facundolucianna/CESE-7maCorte-DCI/3DPictures/01BlueFront.jpg

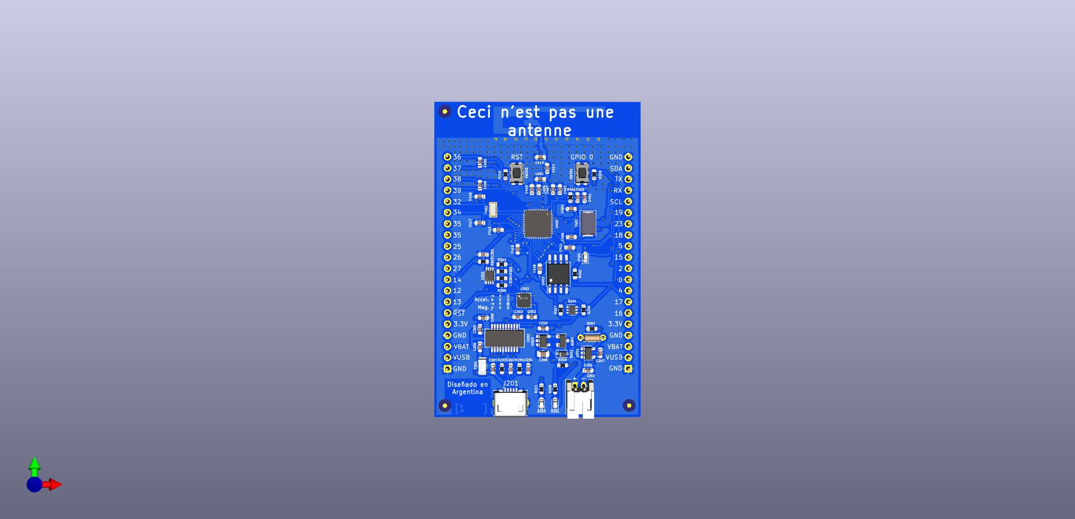
3DPictures/01BlueFront.jpg
