facundolucianna/CESE-7maCorte-DCI/3DPictures/02BlueFrontDetail.jpg

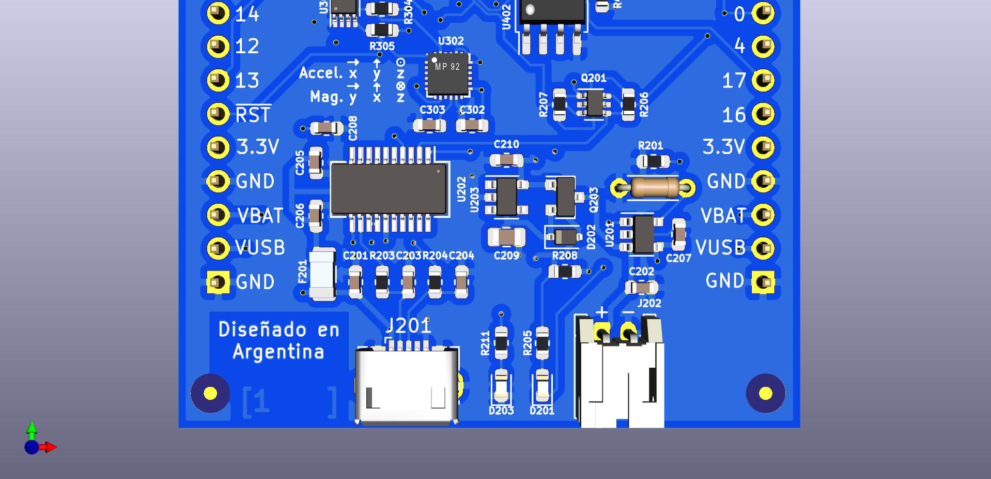
3DPictures/02BlueFrontDetail.jpg
