facundolucianna/CESE-7maCorte-DCI/3DPictures/03BlueBack.jpg

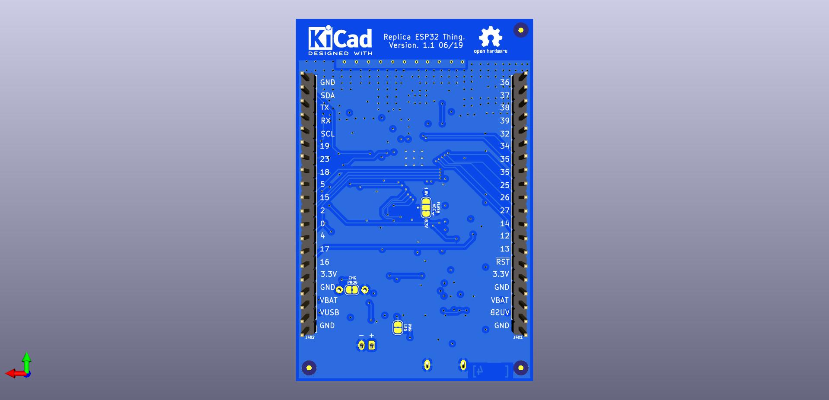
3DPictures/03BlueBack.jpg
