facundolucianna/CESE-7maCorte-DCI/3DPictures/04BlueBackDetail.jpg

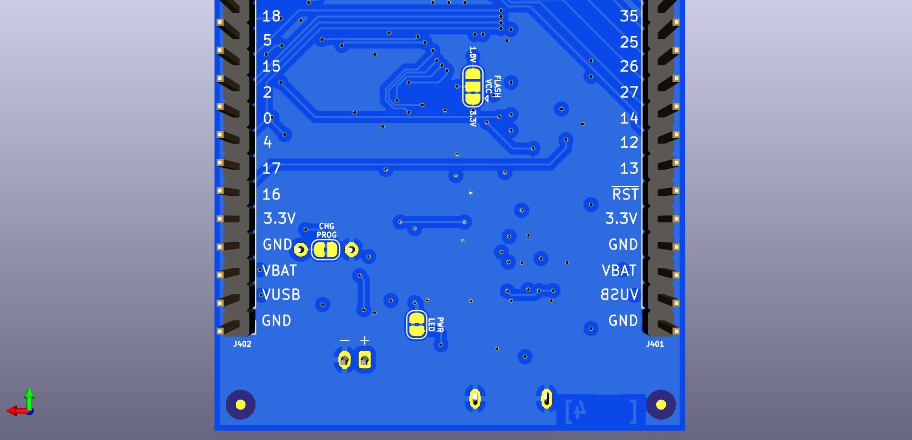
3DPictures/04BlueBackDetail.jpg
