facundolucianna/CESE-7maCorte-DCI/3DPictures/05BlueWeirdAngle.jpg

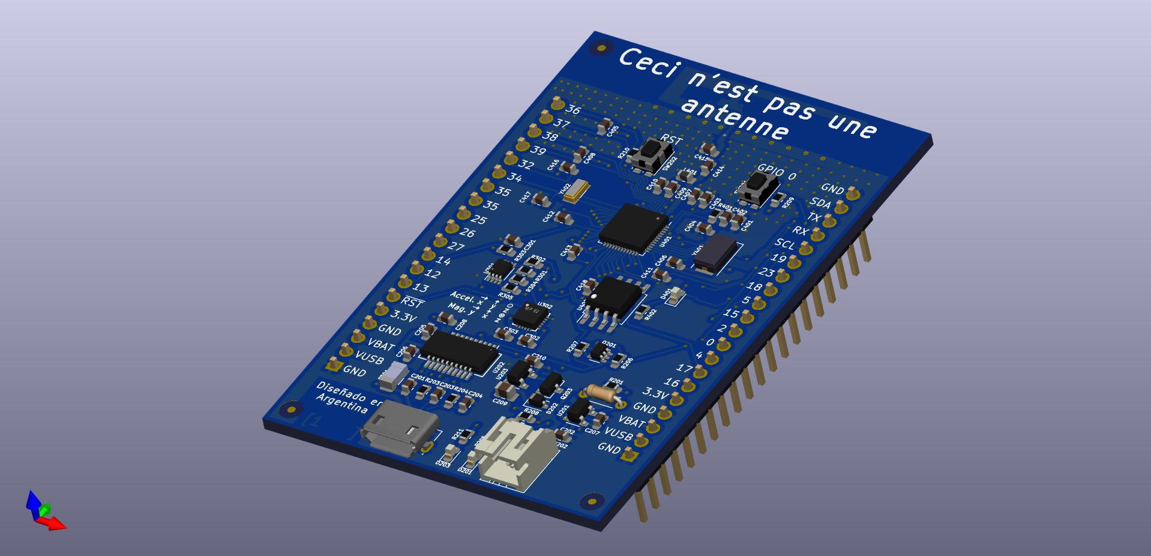
3DPictures/05BlueWeirdAngle.jpg
