facundolucianna/CESE-7maCorte-DCI/3DPictures/06BlueAnotherWeirdAngle.jpg

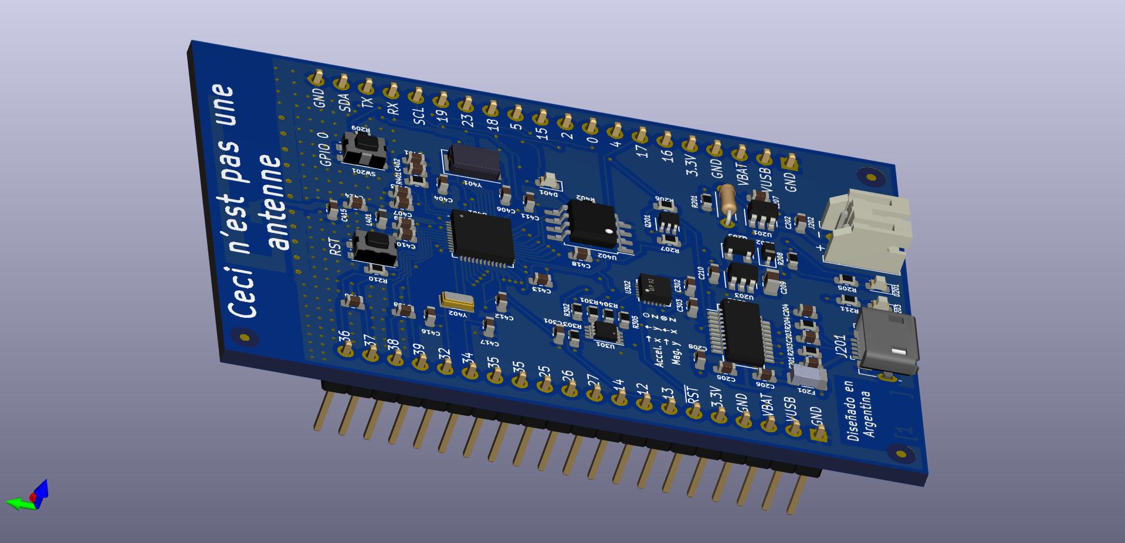
3DPictures/06BlueAnotherWeirdAngle.jpg
