facundolucianna/CESE-7maCorte-DCI/3DPictures/08cheapVersionWeirdAngle.jpg

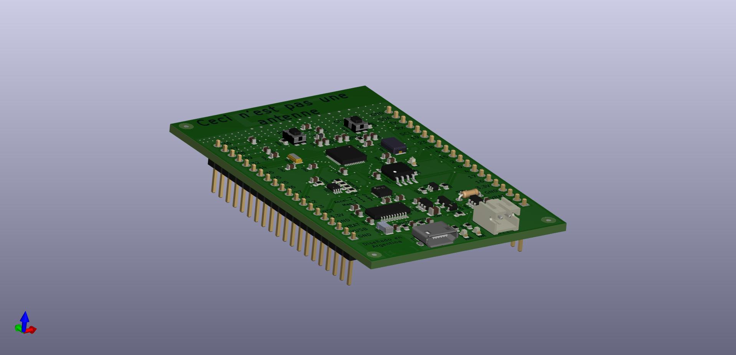
3DPictures/08cheapVersionWeirdAngle.jpg
