facundolucianna/CESE-7maCorte-DCI/3DPictures/09SparfunVersionFront.jpg

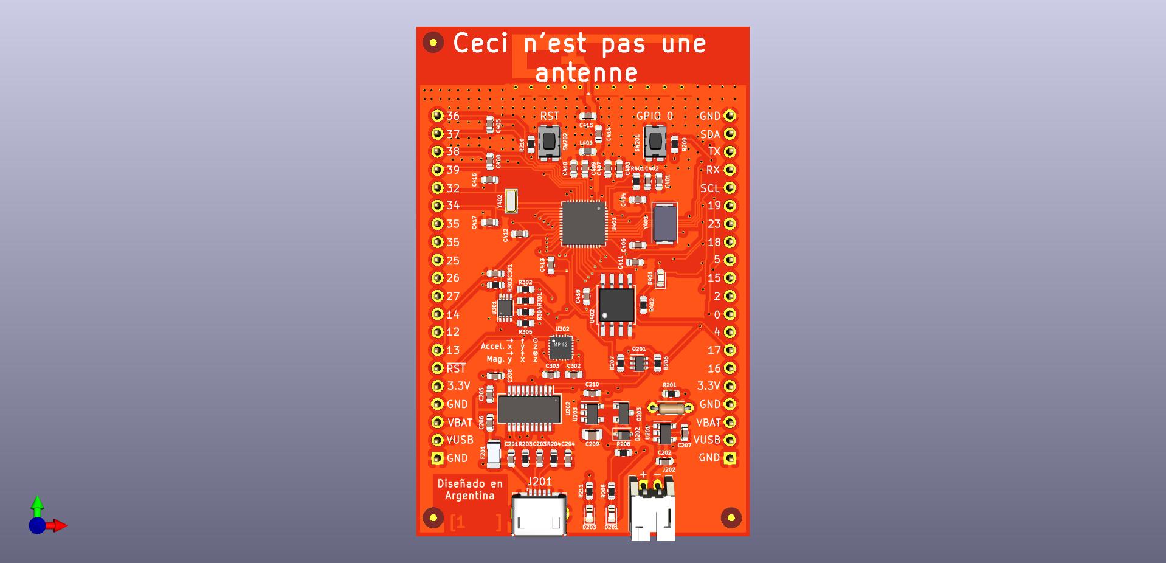
3DPictures/09SparfunVersionFront.jpg
