facundolucianna/CESE-7maCorte-DCI/3DPictures/12YellowVersionFront.jpg

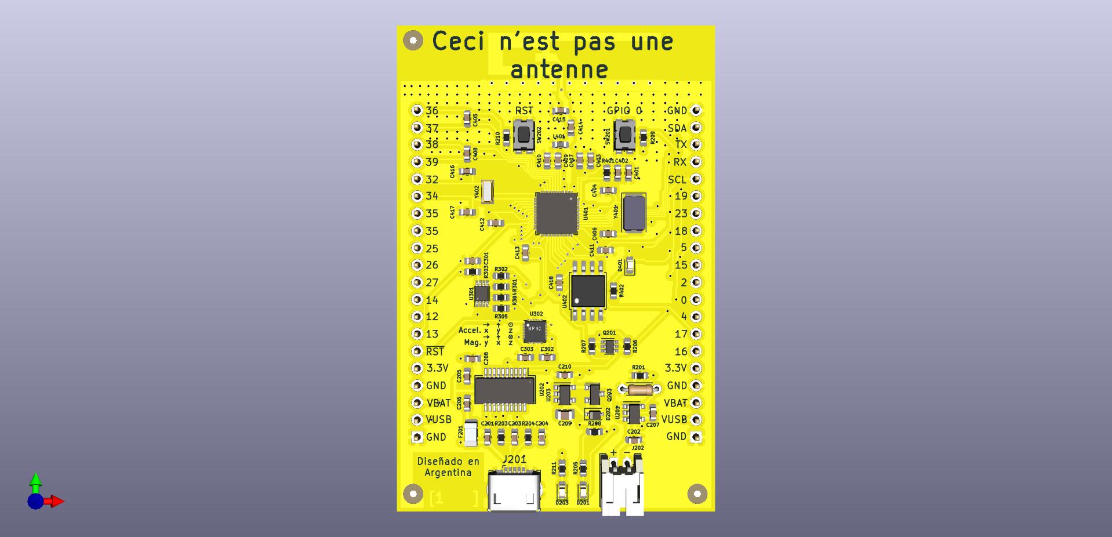
3DPictures/12YellowVersionFront.jpg
